er7-njit/ECET430Project/Initial Component Choices [Depreciated]/Project_Design_Files/Ki_Cad_ProjectFiles/GPSTracker_Design_10-8-24.kicad_sch

## KiCad design Initial Component Choices [Depreciated]/Project_Design_Files/Ki_Cad_ProjectFiles/GPSTracker_Design_10-8-24.kicad_sch (2024-12-22)

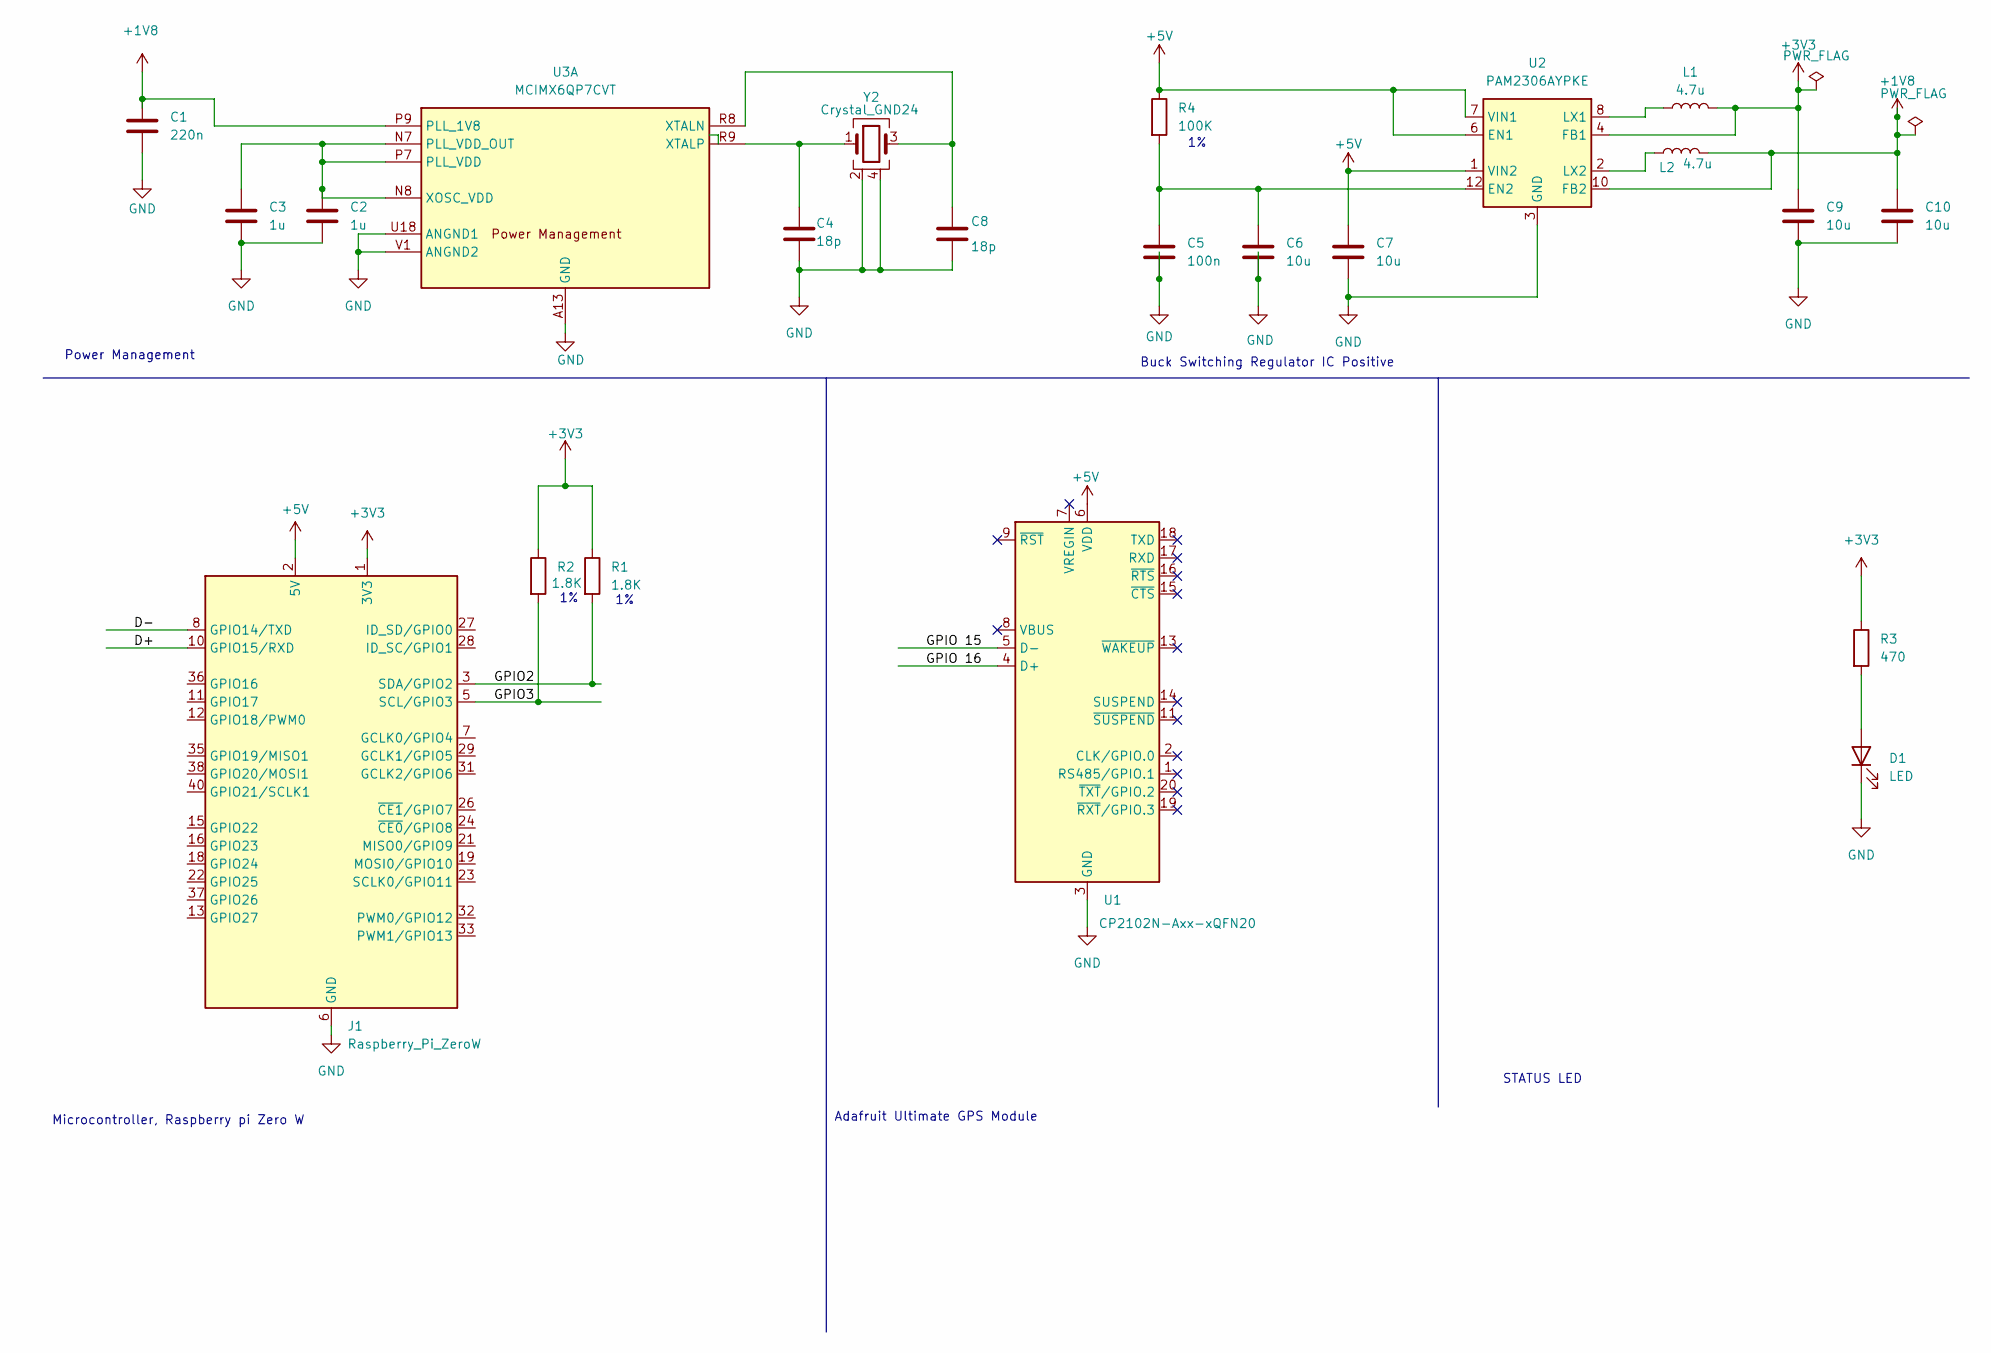
[picture p4: schematic GPSTracker_Design_10-8-24.kicad_sch]

Parts:
C1: 220n
C2, C3: 1u
C4, C8: 18p
C5: 100n
C6, C7, C9, C10: 10u
D1: LED
J1: Raspberry_Pi_ZeroW
L1, L2: 4.7u
R1, R2: 1.8K
R3: 470
R4: 100K
U1: CP2102N-Axx-xQFN20; SiliconLabs_QFN-20-1EP_3x3mm_P0.5mm
U2: PAM2306AYPKE; WDFN-12-1EP_3x3mm_P0.45mm_EP1.7x2.5mm
U3: MCIMX6QP7CVT; BGA-624_21.0x21.0mm_Layout25x25_P0.8mm
Y2: Crystal_GND24

Connections:
+1V8: C1.1, C10.1, L2.2, U2.10 (FB2), U3.J14 (VDD_ARM_IN), U3.K14 (VDD_ARM_IN), U3.L14 (VDD_ARM_IN), U3.M14 (VDD_ARM_IN), U3.N14 (VDD_ARM_IN), U3.P9 (PLL_1V8), U3.P14 (VDD_ARM_IN), U3.R14 (VDD_ARM_IN)
+3V3: C9.1, J1.1 (3V3), J1.17 (3V3), L1.2, R1.1, R2.1, R3.1, U2.4 (FB1)
+5V: C7.1, J1.2 (5V), J1.4 (5V), R4.1, U1.6 (VDD), U2.1 (VIN2), U2.6 (EN1), U2.7 (VIN1)
D+: J1.10 (GPIO15/RXD)
D-: J1.8 (GPIO14/TXD)
GND: C1.2, C2.2, C3.2, C4.2, C5.2, C6.2, C7.2, C8.2, C9.2, C10.2, D1.1 (K), J1.6 (GND), J1.9 (GND), J1.14 (GND), J1.20 (GND), J1.25 (GND), J1.30 (GND), J1.34 (GND), J1.39 (GND), U1.3 (GND), U1.12 (GND), U1.21 (GND), U2.3 (GND), U2.9 (GND), U2.13 (GND), U3.A4 (GND), U3.A8 (GND), U3.A13 (GND), U3.A25 (GND), U3.AA7 (GND), U3.AA10 (GND), U3.AA13 (GND), U3.AA16 (GND), U3.AA19 (GND), U3.AA22 (GND), U3.AB3 (GND), U3.AB24 (GND), U3.AD4 (GND), U3.AD7 (GND), U3.AD10 (GND), U3.AD13 (GND), U3.AD16 (GND), U3.AD19 (GND), U3.AD22 (GND), U3.AE1 (GND), U3.AE25 (GND), U3.B4 (GND), U3.C1 (GND), U3.C4 (GND), U3.C6 (GND), U3.C10 (GND), U3.D3 (GND), U3.D6 (GND), U3.D8 (GND), U3.E5 (GND), U3.E6 (GND), U3.E7 (GND), U3.F5 (GND), U3.F6 (GND), U3.F7 (GND), U3.F8 (GND), U3.G3 (GND), U3.G10 (GND), U3.G19 (GND), U3.H8 (GND), U3.H12 (GND), U3.H15 (GND), U3.H18 (GND), U3.J2 (GND), U3.J8 (GND), U3.J12 (GND), U3.J15 (GND), U3.J18 (GND), U3.K8 (GND), U3.K10 (GND), U3.K12 (GND), U3.K15 (GND), U3.K18 (GND), U3.L2 (GND), U3.L5 (GND), U3.L8 (GND), U3.L10 (GND), U3.L12 (GND), U3.L15 (GND), U3.L18 (GND), U3.M8 (GND), U3.M10 (GND), U3.M12 (GND), U3.M15 (GND), U3.M18 (GND), U3.N8 (GND), U3.N10 (GND), U3.N15 (GND), U3.N18 (GND), U3.P8 (GND), U3.P10 (GND), U3.P12 (GND), U3.P15 (GND), U3.P18 (GND), U3.R8 (GND), U3.R12 (GND), U3.R15 (GND), U3.R17 (GND), U3.T8 (GND), U3.T11 (GND), U3.T12 (GND), U3.T15 (GND), U3.T17 (GND), U3.T19 (GND), U3.U8 (GND), U3.U11 (GND), U3.U12 (GND), U3.U15 (GND), U3.U17 (GND), U3.U18 (ANGND1), U3.U19 (GND), U3.V1 (ANGND2), U3.V8 (GND), U3.V19 (GND), U3.W3 (GND), U3.W7 (GND), U3.W8 (GND), U3.W9 (GND), U3.W10 (GND), U3.W11 (GND), U3.W12 (GND), U3.W13 (GND), U3.W15 (GND), U3.W16 (GND), U3.W17 (GND), U3.W18 (GND), U3.W19 (GND), U3.Y5 (GND), U3.Y24 (GND), Y2.2, Y2.4
GPIO2: J1.3 (SDA/GPIO2), R1.2
GPIO3: J1.5 (SCL/GPIO3), R2.2
GPIO 15: U1.5 (D-)
GPIO 16: U1.4 (D+)
unnamed: C2.1, C3.1, U3.J9 (VDD_HIGH_IN), U3.J16 (VDD_SOC_IN), U3.K16 (VDD_SOC_IN), U3.L9 (VDD_ARM23_IN), U3.L16 (VDD_SOC_IN), U3.M9 (VDD_ARM23_IN), U3.M16 (VDD_SOC_IN), U3.N7 (PLL_VDD_OUT), U3.N8 (GND), U3.N9 (VDD_ARM23_IN), U3.N16 (VDD_SOC_IN), U3.P7 (PLL_VDD), U3.P9 (PLL_1V8), U3.P16 (VDD_SOC_IN), U3.R9 (VDD_ARM23_IN), U3.R16 (VDD_SOC_IN), U3.T9 (VDD_ARM23_IN), U3.T16 (VDD_SOC_IN), U3.U9 (VDD_ARM23_IN), U3.U16 (VDD_SOC_IN)
unnamed: C4.1, U3.J11 (VDD_ARM23_CAP), U3.K11 (VDD_ARM23_CAP), U3.L11 (VDD_ARM23_CAP), U3.M11 (VDD_ARM23_CAP), U3.N11 (VDD_ARM23_CAP), U3.P11 (VDD_ARM23_CAP), U3.R9 (VDD_ARM23_IN), U3.R11 (VDD_ARM23_CAP), Y2.1
unnamed: C5.1, C6.1, R4.2, U2.12 (EN2)
unnamed: C8.1, U3.J13 (VDD_ARM_CAP), U3.K13 (VDD_ARM_CAP), U3.L13 (VDD_ARM_CAP), U3.M13 (VDD_ARM_CAP), U3.N13 (VDD_ARM_CAP), U3.P13 (VDD_ARM_CAP), U3.R8 (GND), U3.R13 (VDD_ARM_CAP), Y2.3
unnamed: D1.2 (A), R3.2
unnamed: L1.1, U2.8 (LX1)
unnamed: L2.1, U2.2 (LX2)

Notes on the sheet:
Power Management
Adafruit Ultimate GPS Module
STATUS LED
Buck Switching Regulator IC Positive
Microcontroller, Raspberry pi Zero W
